rhobison/esport-fi32/docs/3-fota_development_plan.md

# esport-fi32 FOTA Development Plan

**Version:** 2.0
**Date:** 2026-04-06
**Executor:** AI coding agents
**Spec reference:** `docs/1-specification.md`, `docs/2-development_plan.md`

---

## Overview

This plan describes how to add **Firmware Over-The-Air (FOTA) update** capability to the
esport-fi32 firmware.  The implementation is organised as a sequence of self-contained phases
that can be executed at any time after `docs/2-development_plan.md` Phase 10 is complete.
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
