rhobison/esport-fi32/main/inc/config_manager.h

/**
 * \file
 * \brief NVS-backed runtime configuration manager public API.
 *
 * Provides typed getters and setters for every esport-fi32 configuration
 * parameter defined in the firmware specification §3.  Values are persisted
 * to NVS namespace \c esport_cfg and survive reboots.  Factory defaults are
 * applied automatically for any key that is absent or could not be read.
 *
 * \date 2026-03-14
 */

#ifndef CONFIG_MANAGER_H
#define CONFIG_MANAGER_H

#ifdef __cplusplus
extern "C"
{
#endif

//==================================================================================================
// Includes
//==================================================================================================

#include <stdbool.h>
#include <stddef.h>
#include <stdint.h>

#include "esp_err.h"

//==================================================================================================
// Constants/Macros/Datatypes
//==================================================================================================

/** Maximum password length for the config page password (excluding NUL terminator). */
#define CONFIG_MNGR_CFG_PASSWORD_MAX_LEN (63U)

/** Factory default password for the config page HTTP Basic Auth. */
#define CONFIG_MNGR_CFG_PASSWORD_DEFAULT ("esport-fi32")

/** Fixed HTTP Basic Auth username for the config page. */
#define CONFIG_MNGR_CFG_HTTP_USERNAME ("admin")

//==================================================================================================
// Function Prototypes
//==================================================================================================

/**
 * \brief Initialise the NVS partition and load all configuration parameters.
 *
 * Calls \c nvs_flash_init().  If the partition is corrupt
 * (\c ESP_ERR_NVS_NO_FREE_PAGES or \c ESP_ERR_NVS_NEW_VERSION_FOUND),
 * the partition is erased and reinitialised so that factory defaults are
 * applied.  Must be called once from #app_main before any getter or setter
 * is used.
 *
 * \return \c ESP_OK on success, or a non-zero \c esp_err_t on failure.
 */
esp_err_t config_mngr_init(void);

/**
 * \brief Copy the home Wi-Fi SSID into a caller-supplied buffer.
 *
 * \param[out] buf  Destination buffer.
 * \param[in]  len  Size of \p p_buf in bytes (including NUL terminator).
 */
void config_mngr_wifi_ssid_get(char * p_buf, size_t len);

/**
 * \brief Copy the home Wi-Fi WPA2 password into a caller-supplied buffer.
 *
 * \param[out] buf  Destination buffer.
 * \param[in]  len  Size of \p p_buf in bytes (including NUL terminator).
 */
void config_mngr_wifi_password_get(char * p_buf, size_t len);

/**
 * \brief Copy the reward Soft AP SSID into a caller-supplied buffer.
 *
 * \param[out] buf  Destination buffer.
 * \param[in]  len  Size of \p p_buf in bytes (including NUL terminator).
 */
void config_mngr_soft_ap_ssid_get(char * p_buf, size_t len);

/**
 * \brief Copy the reward Soft AP WPA2 password into a caller-supplied buffer.
 *
 * \param[out] buf  Destination buffer.
 * \param[in]  len  Size of \p p_buf in bytes (including NUL terminator).
 */
void config_mngr_soft_ap_password_get(char * p_buf, size_t len);

/**
 * \brief Return the number of seconds credited to the counter per accepted
 * pulse.
 *
 * \return Seconds per pulse (range 1–60).
 */
uint16_t config_mngr_seconds_per_pulse_get(void);

/**
 * \brief Return the internet gate threshold in seconds.
 *
 * Session duration before earned credits start counting down and internet
 * access becomes available.
 *
 * \return Threshold in seconds.
 */
uint32_t config_mngr_internet_gate_threshold_s_get(void);

/**
 * \brief Return the wheel travel distance in centimetres per pulse.
 *
 * \return Centimetres per pulse (>= 1).
 */
uint32_t config_mngr_centimeters_per_pulse_get(void);

/**
 * \brief Return the idle gap that closes an exercise session.
 *
 * \return Idle interval in seconds (range 5–600).
 */
uint16_t config_mngr_idle_session_interval_s_get(void);

/**
 * \brief Return the continuous-pedalling window required to confirm a session.
 *
 * \return Session-start qualification interval in seconds (range 1–300).
 */
uint16_t config_mngr_start_session_interval_s_get(void);

/**
 * \brief Return the minimum time between two accepted pulses.
 *
 * \return Software debounce time in milliseconds (range 10–5000).
 */
uint16_t config_mngr_pulse_debounce_time_ms_get(void);

/**
 * \brief Copy the POSIX timezone string into a caller-supplied buffer.
 *
 * \param[out] buf  Destination buffer.
 * \param[in]  len  Size of \p p_buf in bytes (including NUL terminator).
 */
void config_mngr_timezone_get(char * p_buf, size_t len);

/**
 * \brief Set and persist the home Wi-Fi SSID.
 *
 * \param[in] val  NUL-terminated SSID string (1–32 characters).
 *
 * \return \c ESP_OK on success, \c ESP_ERR_INVALID_ARG if \p val is out of
 *         the allowed length range, or an NVS error code on write failure.
 */
esp_err_t config_mngr_wifi_ssid_set(const char * p_val);

/**
 * \brief Set and persist the home Wi-Fi WPA2 password.
 *
 * \param[in] val  NUL-terminated password string (0–64 characters).
 *
 * \return \c ESP_OK on success, \c ESP_ERR_INVALID_ARG if \p val is out of
 *         the allowed length range, or an NVS error code on write failure.
 */
esp_err_t config_mngr_wifi_password_set(const char * p_val);

/**
 * \brief Set and persist the reward Soft AP SSID.
 *
 * \param[in] val  NUL-terminated SSID string (1–32 characters).
 *
 * \return \c ESP_OK on success, \c ESP_ERR_INVALID_ARG if \p val is out of
 *         the allowed length range, or an NVS error code on write failure.
 */
esp_err_t config_mngr_soft_ap_ssid_set(const char * p_val);

/**
 * \brief Set and persist the reward Soft AP WPA2 password.
 *
 * \param[in] val  NUL-terminated password string (0–64 characters).
 *
 * \return \c ESP_OK on success, \c ESP_ERR_INVALID_ARG if \p val is out of
 *         the allowed length range, or an NVS error code on write failure.
 */
esp_err_t config_mngr_soft_ap_password_set(const char * p_val);

/**
 * \brief Set and persist the seconds credited per accepted pulse.
 *
 * \param[in] val  Seconds per pulse (valid range: 1–60).
 *
 * \return \c ESP_OK on success, \c ESP_ERR_INVALID_ARG if \p val is outside
 *         the valid range, or an NVS error code on write failure.
 */
esp_err_t config_mngr_seconds_per_pulse_set(uint16_t val);

/**
 * \brief Set and persist the internet gate threshold.
 *
 * Session duration in seconds before earned credits start counting down
 * and internet access becomes available.
 *
 * \param[in] val  Gate threshold in seconds (range: 0–UINT32_MAX).
 *
 * \return \c ESP_OK on success, or an NVS error code on write failure.
 */
esp_err_t config_mngr_internet_gate_threshold_s_set(uint32_t val);

/**
 * \brief Set and persist the wheel travel distance per pulse.
 *
 * \param[in] val  Centimetres per pulse (valid range: 1–UINT32_MAX).
 *
 * \return \c ESP_OK on success, \c ESP_ERR_INVALID_ARG if \p val is 0,
 *         or an NVS error code on write failure.
 */
esp_err_t config_mngr_centimeters_per_pulse_set(uint32_t val);

/**
 * \brief Set and persist the idle gap that closes a session.
 *
 * \param[in] val  Idle interval in seconds (valid range: 5–600).
 *
 * \return \c ESP_OK on success, \c ESP_ERR_INVALID_ARG if \p val is outside
 *         the valid range, or an NVS error code on write failure.
 */
esp_err_t config_mngr_idle_session_interval_s_set(uint16_t val);

/**
 * \brief Set and persist the session-start qualification window.
 *
 * \param[in] val  Qualification interval in seconds (valid range: 1–300).
 *
 * \return \c ESP_OK on success, \c ESP_ERR_INVALID_ARG if \p val is outside
 *         the valid range, or an NVS error code on write failure.
 */
esp_err_t config_mngr_start_session_interval_s_set(uint16_t val);

/**
 * \brief Set and persist the pulse debounce time.
 *
 * \param[in] val  Debounce time in milliseconds (valid range: 10–5000).
 *
 * \return \c ESP_OK on success, \c ESP_ERR_INVALID_ARG if \p val is outside
 *         the valid range, or an NVS error code on write failure.
 */
esp_err_t config_mngr_pulse_debounce_time_ms_set(uint16_t val);

/**
 * \brief Set and persist the POSIX timezone string.
 *
 * \param[in] val  NUL-terminated POSIX TZ string (1–63 characters).
 *
 * \return \c ESP_OK on success, \c ESP_ERR_INVALID_ARG if \p val is out of
 *         the allowed length range, or an NVS error code on write failure.
 */
esp_err_t config_mngr_timezone_set(const char * p_val);
/**
 * \brief Return the reward AP idle throughput threshold in kbps.
 *
 * If combined RX+TX throughput on the reward AP drops below this value for
 * more than #config_mngr_soft_ap_idle_throughput_timeout_s_get() consecutive
 * seconds, the time counter pauses decrementing.
 *
 * \return Threshold in kbps (range 0-65535; 0 = pause immediately).
 */
uint16_t  config_mngr_soft_ap_dec_threshold_kbps_get(void);

/**
 * \brief Set and persist the reward AP idle throughput threshold.
 *
 * \param[in] val  Threshold in kbps (range 0-65535).
 *
 * \return \c ESP_OK on success, or an NVS error code on write failure.
 */
esp_err_t config_mngr_soft_ap_dec_threshold_kbps_set(uint16_t val);

/**
 * \brief Return the number of consecutive below-threshold seconds before the
 * countdown pauses.
 *
 * \return Timeout in seconds (range 0-65535; 0 = pause on first below-threshold
 *         tick).
 */
uint16_t config_mngr_soft_ap_idle_throughput_timeout_s_get(void);

/**
 * \brief Set and persist the below-threshold idle timeout.
 *
 * \param[in] val  Timeout in seconds (range 0-65535).
 *
 * \return \c ESP_OK on success, or an NVS error code on write failure.
 */
esp_err_t config_mngr_soft_ap_idle_throughput_timeout_s_set(uint16_t val);

/**
 * \brief Return the minimum instantaneous speed required to earn time credits.
 *
 * Speed is expressed in km/h x 10 (e.g. 30 = 3.0 km/h).  A value of \c 0
 * disables the gate: all pulses earn credits regardless of speed.
 *
 * \return Minimum speed threshold in km/h x 10 (range 0-65535).
 */
uint16_t config_mngr_min_speed_to_increment_time_kmh_x10_get(void);

/**
 * \brief Set and persist the minimum speed threshold for time credit earning.
 *
 * \param[in] val  Threshold in km/h x 10 (range 0-65535; 0 = gate disabled).
 *
 * \return \c ESP_OK on success, or an NVS error code on write failure.
 */
esp_err_t config_mngr_min_speed_to_increment_time_kmh_x10_set(uint16_t val);

/**
 * \brief Return the persisted reward time counter value in seconds.
 *
 * This value is saved to NVS periodically and on counter reaching 0.  On
 * boot, the time counter module reads this value to restore the counter.
 *
 * \return Reward counter in seconds (0 when no time is stored).
 */
uint32_t config_mngr_reward_counter_s_get(void);

/**
 * \brief Set and persist the reward time counter value.
 *
 * Called by the time counter module to save the live counter to NVS.  The
 * full uint32_t range is valid.
 *
 * \param[in] val  Counter value in seconds (range 0–UINT32_MAX).
 *
 * \return \c ESP_OK on success, or an NVS error code on write failure.
 */
esp_err_t config_mngr_reward_counter_s_set(uint32_t val);

/**
 * \brief Erase all configuration keys and restore factory defaults.
 *
 * Erases the entire \c esport_cfg NVS namespace, then writes all factory
 * default values and commits.  This is the in-firmware equivalent of a
 * factory reset for configuration parameters only (session log is not
 * affected).
 *
 * \return \c ESP_OK on success, or a non-zero \c esp_err_t on failure.
 */
bool      config_mngr_buzzer_enabled_get(void);
esp_err_t config_mngr_buzzer_enabled_set(bool b_enabled);

/**
 * \brief Return the low-speed buzzer delay threshold in seconds.
 *
 * The speed-low beep begins only after the speed has been continuously
 * below the minimum threshold for this many consecutive seconds.  A value
 * of \c 0 triggers the beep immediately on the first below-threshold tick.
 *
 * \return Threshold in seconds (range 0–65535; default 3).
 */
uint16_t config_mngr_low_speed_buzzer_threshold_s_get(void);

/**
 * \brief Set and persist the low-speed buzzer delay threshold.
 *
 * \param[in] val  Threshold in seconds (range 0–65535; 0 = immediate).
 *
 * \return \c ESP_OK on success, or an NVS error code on write failure.
 */
esp_err_t config_mngr_low_speed_buzzer_threshold_s_set(uint16_t val);

/**
 * \brief Copy the config page HTTP Basic Auth password into a caller-supplied buffer.
 *
 * Falls back to #CONFIG_MNGR_CFG_PASSWORD_DEFAULT if the NVS key is absent.
 *
 * \param[out] p_buf  Destination buffer.
 * \param[in]  len    Size of \p p_buf in bytes (including NUL terminator).
 *
 * \return \c ESP_OK on success, or \c ESP_ERR_INVALID_ARG if \p p_buf or \p len are invalid.
 */
esp_err_t config_mngr_cfg_password_get(char * p_buf, size_t len);

/**
 * \brief Persist a new config page HTTP Basic Auth password.
 *
 * \param[in] p_password  New password string (1–#CONFIG_MNGR_CFG_PASSWORD_MAX_LEN chars).
 *
 * \return \c ESP_OK on success, \c ESP_ERR_INVALID_ARG if length is out of range,
 *         or an NVS error code on write failure.
 */
esp_err_t config_mngr_cfg_password_set(const char * p_password);

/**
 * \brief Check whether \p p_password matches the stored config page password.
 *
 * The supplied password is never logged.
 *
 * \param[in] p_password  Candidate password string.
 *
 * \return \c true if the password matches, \c false otherwise.
 */
bool config_mngr_cfg_credentials_check(const char * p_password);

esp_err_t config_mngr_reset_to_defaults(void);

/**
 * \brief Return whether the activity-credit buzzer beep is enabled.
 *
 * When \c false, #buzzer_pattern_play is not called on activity credit; all
 * other crediting behaviour is unchanged.  Defaults to \c true when the
 * NVS key is absent.
 *
 * \return \c true if the activity-credit beep is enabled, \c false otherwise.
 */
bool config_mngr_activity_credit_buzzer_en_get(void);

/**
 * \brief Enable or disable the activity-credit buzzer beep.
 *
 * \param[in] b_enabled  \c true to enable the beep; \c false to suppress it.
 *
 * \return \c ESP_OK on success, or an NVS error code on write failure.
 */
esp_err_t config_mngr_activity_credit_buzzer_en_set(bool b_enabled);

#ifdef __cplusplus
}
#endif

#endif // CONFIG_MANAGER_H

/*** end of file ***/
