rhobison/esport-fi32/main/src/http_server_ota.c

/**
 * \file
 * \brief HTTP OTA handler implementation.
 *
 * Provides four URI handlers that implement a Basic-Auth-protected firmware
 * upload page (GET /ota), firmware upload endpoint (POST /ota), and OTA
 * password management (GET /ota/pwd, POST /ota/pwd).
 *
 * Basic Auth credentials: username = "admin" (hardcoded), password = stored
 * in NVS namespace \c esport_ota via #ota_mngr_credentials_check().
 *
 * \date 2026-04-06
 */

//==================================================================================================
// Includes
//==================================================================================================

#include "http_server_ota.h"
#include "http_server_utils.h"
#include "ota_manager.h"

#include <string.h>
#include <stdio.h>
#include <stdint.h>

#include "esp_log.h"

//==================================================================================================
// Internal Constants/Macros/Datatypes
//==================================================================================================

/** Receive buffer size for POST /ota body chunks (bytes). */
#define OTA_MNGR_RECV_BUF_SIZE (1024U)

/** Maximum length including NUL for the Authorization header value. */
#define HTTP_SRV_OTA_AUTH_HDR_MAX (256U)

/** Minimum length of "Basic " prefix in the Authorization header. */
#define HTTP_SRV_OTA_BASIC_PREFIX_LEN (6U)

/** Maximum length of the decoded "user:password" string. */
#define HTTP_SRV_OTA_DECODED_MAX (192U)

/** Maximum length of a single URL-decoded form field. */
#define HTTP_SRV_OTA_FIELD_MAX (OTA_MNGR_PASSWORD_MAX_LEN + 1U)

//==================================================================================================
// Variables/Data
//==================================================================================================

/** Module log tag. */
static const char * gp_tag = "http_server_ota";

//==================================================================================================
// Internal Function Prototypes
//==================================================================================================

static bool http_srv_ota_auth_check(httpd_req_t * p_req);

//==================================================================================================
// Public Functions
//==================================================================================================

/**
 * \brief Handle GET /ota -- serve the firmware upload page.
 *
 * \param[in] p_req  HTTP request handle.
 *
 * \return \c ESP_OK always.
 */
esp_err_t http_srv_ota_get_handler(httpd_req_t * p_req)
{
    if (!http_srv_ota_auth_check(p_req))
    {
        return ESP_OK;
    }

    char version[32];
    ota_mngr_running_version_get(version, sizeof(version));

    (void)httpd_resp_set_type(p_req, "text/html");

    (void)httpd_resp_sendstr_chunk(p_req,
        "<!DOCTYPE html><html><head>"
        "<meta charset=\"UTF-8\">"
        "<meta name=\"viewport\" content=\"width=device-width,initial-scale=1\">"
        "<title>ESPort-fi32 -- Firmware Update</title>"
        "<style>"
        "body{font-family:sans-serif;max-width:600px;margin:2em auto;padding:0 1em;}"
        "h1{font-size:1.3em;}"
        "h2{font-size:1.1em;margin-top:1.5em;}"
        ".card{border:1px solid #ccc;border-radius:6px;padding:1em;margin:1em 0;}"
        "input[type=file]{display:block;margin:0.5em 0;}"
        "button,.btn{background:#2a6db5;color:#fff;border:none;padding:0.5em 1.2em;"
        "border-radius:4px;cursor:pointer;text-decoration:none;display:inline-block;}"
        "button:hover,.btn:hover{background:#1e5490;}"
        "progress{width:100%;margin:0.5em 0;}"
        "#upload-status{margin-top:0.5em;font-weight:bold;}"
        "nav a{margin-right:1em;}"
        "</style>"
        "</head><body>"
        "<h1>ESPort-fi32 -- Firmware Update</h1>");

    /* Running firmware section */
    static char buf[128];
    (void)snprintf(buf, sizeof(buf),
        "<div class=\"card\"><h2>Running Firmware</h2>"
        "<p>Version: <strong>%s</strong></p></div>",
        version);
    (void)httpd_resp_sendstr_chunk(p_req, buf);

    /* Upload section */
    (void)httpd_resp_sendstr_chunk(p_req,
        "<div class=\"card\"><h2>Upload New Firmware</h2>"
        "<progress id=\"upload-progress\" value=\"0\" max=\"100\" "
        "style=\"display:none;\"></progress>"
        "<input type=\"file\" id=\"fw-file\" accept=\".bin\">"
        "<button id=\"flash-btn\">Flash Firmware</button>"
        "<div id=\"upload-status\"></div>"
        "</div>");

    /* OTA password section */
    (void)httpd_resp_sendstr_chunk(p_req, "<div class=\"card\"><h2>OTA Password</h2>"
                                          "<p><a href=\"/ota/pwd\">Change OTA password</a></p>"
                                          "</div>");

    /* Navigation */
    (void)httpd_resp_sendstr_chunk(p_req, "<nav><a class=\"btn\" href=\"/\">Dashboard</a></nav>");

    /* Inline upload script */
    (void)httpd_resp_sendstr_chunk(p_req,
        "<script>"
        "document.getElementById('flash-btn').addEventListener('click',function(){"
        "var f=document.getElementById('fw-file').files[0];"
        "if(!f){document.getElementById('upload-status').textContent="
        "'Please select a .bin file.';return;}"
        "var xhr=new XMLHttpRequest();"
        "xhr.open('POST','/ota',true);"
        "xhr.setRequestHeader('Content-Type','application/octet-stream');"
        "xhr.upload.onprogress=function(e){"
        "if(e.lengthComputable){"
        "var p=document.getElementById('upload-progress');"
        "p.style.display='block';"
        "p.value=e.loaded;p.max=e.total;}"
        "};"
        "xhr.onload=function(){"
        "document.getElementById('upload-status').textContent="
        "(xhr.status===200)?'Update successful. Rebooting...':"
        "'Error: '+xhr.responseText;"
        "};"
        "xhr.onerror=function(){"
        "document.getElementById('upload-status').textContent="
        "'Connection lost (device is rebooting).';"
        "};"
        "xhr.send(f);"
        "});"
        "</script>"
        "</body></html>");

    (void)httpd_resp_sendstr_chunk(p_req, NULL);
    return ESP_OK;
}

//--------------------------------------------------------------------------------------------------

/**
 * \brief Handle POST /ota -- receive and flash a firmware binary.
 *
 * \param[in] p_req  HTTP request handle.
 *
 * \return \c ESP_OK on success (device reboots), \c ESP_FAIL on error.
 */
esp_err_t http_srv_ota_post_handler(httpd_req_t * p_req)
{
    if (!http_srv_ota_auth_check(p_req))
    {
        return ESP_OK;
    }

    /* Determine image size from Content-Length header if available. */
    char   cl_buf[32];
    size_t image_size = 0U;
    if (0U < httpd_req_get_hdr_value_len(p_req, "Content-Length"))
    {
        if (ESP_OK == httpd_req_get_hdr_value_str(p_req, "Content-Length", cl_buf, sizeof(cl_buf)))
        {
            image_size = (size_t)strtoul(cl_buf, NULL, 10);
        }
    }

    esp_err_t ret = ota_mngr_begin(image_size);
    if (ESP_OK != ret)
    {
        ESP_LOGE(gp_tag, "ota_mngr_begin failed: %s", esp_err_to_name(ret));
        (void)httpd_resp_set_status(p_req, "500 Internal Server Error");
        (void)httpd_resp_sendstr(p_req, esp_err_to_name(ret));
        return ESP_FAIL;
    }

    static char buf[OTA_MNGR_RECV_BUF_SIZE];
    int         received;

    for (;;)
    {
        received = httpd_req_recv(p_req, buf, OTA_MNGR_RECV_BUF_SIZE);

        if (0 == received)
        {
            /* All data received. */
            break;
        }

        if (received < 0)
        {
            ESP_LOGE(gp_tag, "httpd_req_recv error: %d", received);
            (void)ota_mngr_abort();
            (void)httpd_resp_set_status(p_req, "500 Internal Server Error");
            (void)httpd_resp_sendstr(p_req, "Receive error");
            return ESP_FAIL;
        }

        ret = ota_mngr_write(buf, (size_t)received);
        if (ESP_OK != ret)
        {
            ESP_LOGE(gp_tag, "ota_mngr_write failed: %s", esp_err_to_name(ret));
            (void)ota_mngr_abort();
            (void)httpd_resp_set_status(p_req, "500 Internal Server Error");
            (void)httpd_resp_sendstr(p_req, esp_err_to_name(ret));
            return ESP_FAIL;
        }
    }

    ret = ota_mngr_end();
    if (ESP_OK != ret)
    {
        ESP_LOGE(gp_tag, "ota_mngr_end failed: %s", esp_err_to_name(ret));
        (void)httpd_resp_set_status(p_req, "500 Internal Server Error");
        (void)httpd_resp_sendstr(p_req, esp_err_to_name(ret));
        return ESP_FAIL;
    }

    (void)httpd_resp_sendstr(p_req, "OK");

    /* Activate reboots the device; on failure it returns. */
    ota_mngr_activate();

    /* Only reached if activation failed. */
    (void)httpd_resp_set_status(p_req, "500 Internal Server Error");
    (void)httpd_resp_sendstr(p_req, "Activation failed");
    return ESP_FAIL;
}

//--------------------------------------------------------------------------------------------------
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
