rhobison/esport-fi32/main/src/ota_manager.c

/**
 * \file
 * \brief OTA firmware update manager implementation.
 *
 * Wraps ESP-IDF esp_ota_ops to provide a simple write-chunk state machine
 * used by the HTTP OTA handler.  Manages the OTA password in NVS namespace
 * \c esport_ota and marks the running firmware valid on every boot to cancel
 * any pending rollback window.
 *
 * \date 2026-04-06
 */

//==================================================================================================
// Includes
//==================================================================================================

#include "ota_manager.h"

#include <string.h>
#include <stdio.h>

#include "esp_app_desc.h"
#include "esp_log.h"
#include "esp_ota_ops.h"
#include "esp_system.h"
#include "nvs.h"
#include "nvs_flash.h"

//==================================================================================================
// Internal Constants/Macros/Datatypes
//==================================================================================================

/** NVS namespace used by the OTA manager. */
#define OTA_MNGR_NVS_NAMESPACE ("esport_ota")

/** NVS key for the OTA Basic Auth password. */
#define OTA_MNGR_NVS_KEY_PWD ("ota_pwd")

/** Default OTA password applied when the NVS key is absent. */
#define OTA_MNGR_DEFAULT_PWD ("esport-fi32")

//==================================================================================================
// Variables/Data
//==================================================================================================

/** Module log tag. */
static const char * gp_tag = "ota_manager";

/** Current OTA state machine state. */
static ota_mngr_state_t g_state = OTA_MNGR_STATE_IDLE;

/** Active OTA write handle (valid only in RECEIVING / VERIFYING states). */
static esp_ota_handle_t g_ota_handle = 0;

/** Target partition for the current update (non-NULL in RECEIVING / VERIFYING / READY). */
static const esp_partition_t * gp_update_partition = NULL;

/** Open NVS handle for the esport_ota namespace, set by #ota_mngr_init(). */
static nvs_handle_t g_nvs_handle = 0;
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
